PEOPLE-INSIDE/people-inside/projects/img/us.jpg

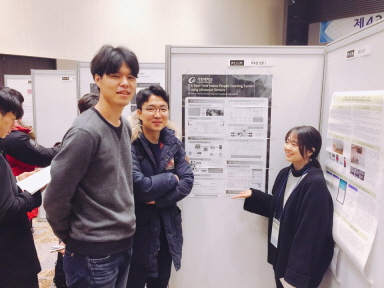
projects/img/us.jpg
